mikelawrence/RPi-HAT-RGBW-LED-Controller/code-light/PCA9685.py

# Copyright (c) 2016 Adafruit Industries
# Author: Tony DiCola
#
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
# Modified by Mike Lawrence 2018
#
# Now most methods use writeList() instead of write8() so a single transaction
# is used instead of multiple single byte transactions.
#
# The AI bit is now set in the MODE1 register which turns on the auto-increment
# address counter. This makes multiple byte transactions work as intended.
#
# Added the set_multiple_pwm() method that writes the LED On and LED Off
# values for multiple PWM channels starting with CH0. This is particuarly handy
# when this device is used to control an RGB LED using CH0-CH2 since now all
# RGB PWM values change simultaneously.
#
from __future__ import division
import logging
import time
import math

# Registers/etc:
PCA9685_ADDRESS    = 0x40
MODE1              = 0x00
MODE2              = 0x01
SUBADR1            = 0x02
SUBADR2            = 0x03
SUBADR3            = 0x04
PRESCALE           = 0xFE
LED0_ON_L          = 0x06
LED0_ON_H          = 0x07
LED0_OFF_L         = 0x08
LED0_OFF_H         = 0x09
ALL_LED_ON_L       = 0xFA
ALL_LED_ON_H       = 0xFB
ALL_LED_OFF_L      = 0xFC
ALL_LED_OFF_H      = 0xFD

# Bits:
RESTART            = 0x80
SLEEP              = 0x10
ALLCALL            = 0x01
AI                 = 0x20
INVRT              = 0x10
OUTDRV             = 0x04


logger = logging.getLogger(__name__)


def software_reset(i2c=None, **kwargs):
    """Sends a software reset (SWRST) command to all PCA9685's on the bus."""
    # Setup I2C interface for device 0x00 to talk to all of them.
    if i2c is None:
        import Adafruit_GPIO.I2C as I2C
        i2c = I2C
    self._device = i2c.get_i2c_device(0x00, **kwargs)
    self._device.writeRaw8(0x06)  # SWRST


class PCA9685(object):
    """PCA9685 PWM LED/servo controller."""

    def __init__(self, address=PCA9685_ADDRESS, i2c=None, **kwargs):
        """Initialize the PCA9685."""
        # Setup I2C interface for the device.
        if i2c is None:
            import Adafruit_GPIO.I2C as I2C
            i2c = I2C
        self._device = i2c.get_i2c_device(address, **kwargs)
        self.set_all_pwm(0, 0)
        self._device.write8(MODE2, OUTDRV)
        self._device.write8(MODE1, ALLCALL | AI)
        time.sleep(0.005)  # wait for oscillator
        mode1 = self._device.readU8(MODE1)
        mode1 = mode1 & ~SLEEP  # wake up (reset sleep)
        self._device.write8(MODE1, mode1)
        time.sleep(0.005)  # wait for oscillator

    def set_pwm_freq(self, freq_hz):
        """Set the PWM frequency to the provided value in hertz."""
        prescaleval = 25000000.0    # 25MHz
        prescaleval /= 4096.0       # 12-bit
        prescaleval /= float(freq_hz)
        prescaleval -= 1.0
        logger.debug('Setting PWM frequency to {0} Hz'.format(freq_hz))
        logger.debug('Estimated pre-scale: {0}'.format(prescaleval))
        prescale = int(math.floor(prescaleval + 0.5))
        logger.debug('Final pre-scale: {0}'.format(prescale))
        oldmode = self._device.readU8(MODE1);
        newmode = (oldmode & 0x7F) | 0x10    # sleep
        self._device.write8(MODE1, newmode)  # go to sleep
        self._device.write8(PRESCALE, prescale)
        self._device.write8(MODE1, oldmode)
        time.sleep(0.005)
        self._device.write8(MODE1, oldmode | 0x80)

    def set_pwm(self, channel, on, off):
        """Sets a single PWM channel."""
        data = [on & 0xFF, on >> 8, off & 0xFF, off >> 8]
        self._device.writeList(LED0_ON_L+4*channel, data)

    def set_pwm_on(self, channel, on):
        """Sets ON time for a single PWM channel."""
        data = [on & 0xFF, on >> 8]
        self._device.writeList(LED0_ON_L+4*channel, data)

    def set_pwm_off(self, channel, off):
        """Sets OFF time for a single PWM channel."""
        data = [off & 0xFF, off >> 8]
        self._device.writeList(LED0_OFF_L+4*channel, data)

    def set_multiple_pwm(self, values):
        """Sets the PWM for multiple channels starting with channel 0."""
        data = []
        for i in range(len(values)):
            data.append(0)                  # ON lower bits
            data.append(0)                  # ON upper Bits
            data.append(values[i] & 0xFF)   # OFF lower bits
            data.append(values[i] >> 8)     # OFF upper bits
        self._device.writeList(LED0_ON_L, data)

    def set_all_pwm(self, on, off):
        """Sets all PWM channels."""
        data = [on & 0xFF, on >> 8, off & 0xFF, off >> 8]
        self._device.writeList(ALL_LED_ON_L, data)
