mikelawrence/RPi-HAT-RGBW-LED-Controller/code-test/timer.py

#!/usr/bin/python3
# The license of this file is unknown.
# The code came from Stack Overflow
# https://stackoverflow.com/questions/12435211/python-threading-timer-repeat-function-every-n-seconds

from threading import Timer

class InfiniteTimer():
    """A Timer class that does not stop, unless you want it to."""

    def __init__(self, seconds, target):
        self._should_continue = False
        self.is_running = False
        self.seconds = seconds
        self.target = target
        self.thread = None

    def _handle_target(self):
        self._start_timer()
        self.is_running = True
        self.target()
        self.is_running = False

    def _start_timer(self):
        if self._should_continue: # Code could have been running when cancel was called.
            self.thread = Timer(self.seconds, self._handle_target)
            self.thread.start()

    def start(self):
        if not self._should_continue and not self.is_running:
            self._should_continue = True
            self._start_timer()
        else:
            print("Timer already started or running, please wait if you're restarting.")

    def cancel(self):
        if self.thread is not None:
            self._should_continue = False # Just in case thread is running and cancel fails.
            self.thread.cancel()
        else:
            print("Timer never started or failed to initialize.")
